imjacobestep/smart-study-lamp/tesseract example.jpg

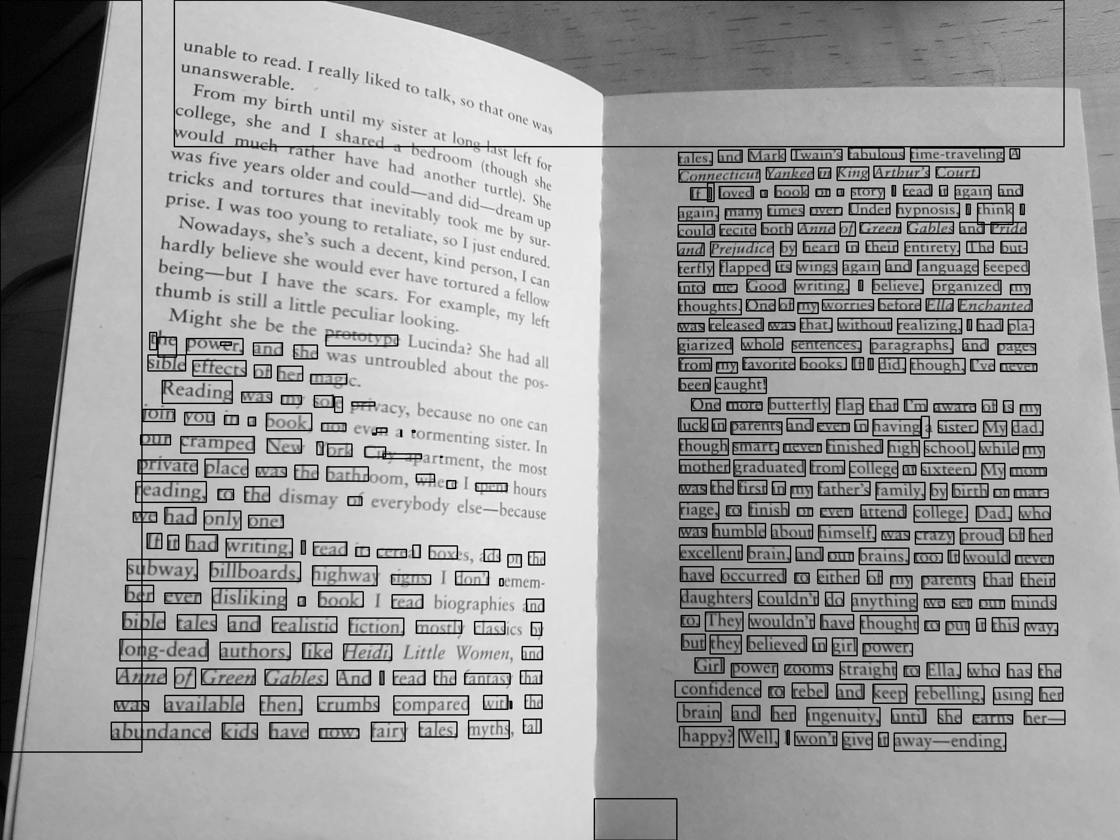
tesseract example.jpg
