imjacobestep/smart-study-lamp/test_code/past_camera_test/photos/images_crop/1.jpg

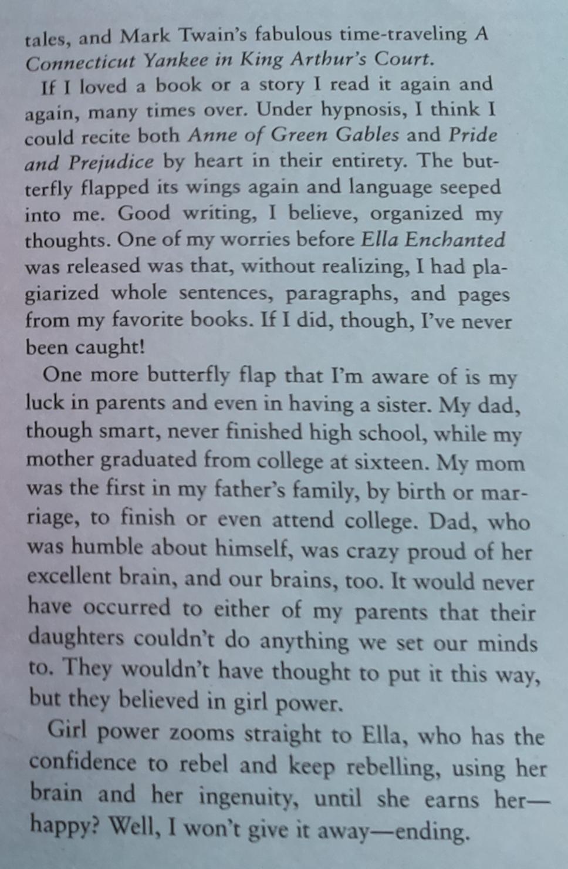
test_code/past_camera_test/photos/images_crop/1.jpg
