imjacobestep/smart-study-lamp/test_code/past_camera_test/photos/photos with lens 1/test5.jpg

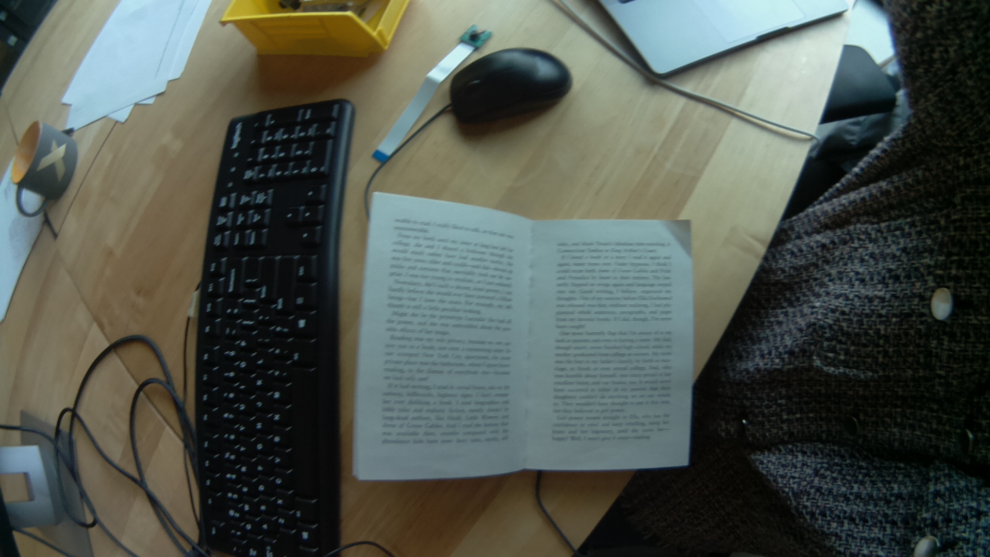
test_code/past_camera_test/photos/photos with lens 1/test5.jpg
