imjacobestep/smart-study-lamp/test_code/past_camera_test/photos/photos with lens 2/img0_stand.jpg

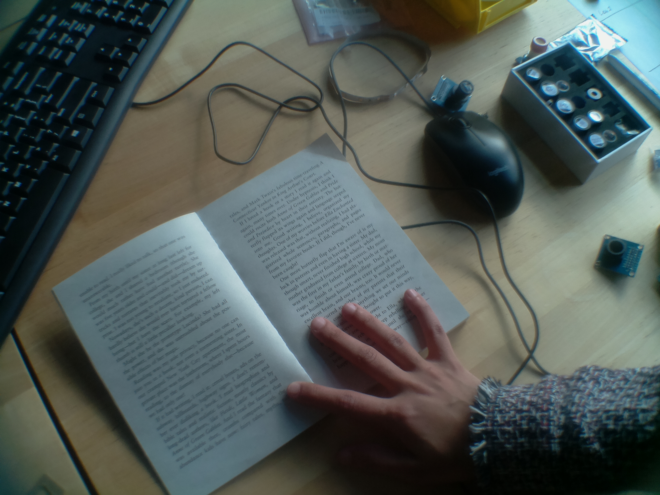
test_code/past_camera_test/photos/photos with lens 2/img0_stand.jpg
