imjacobestep/smart-study-lamp/test_code/past_camera_test/photos/photos with raspberry pi cam/img3_stand.jpg

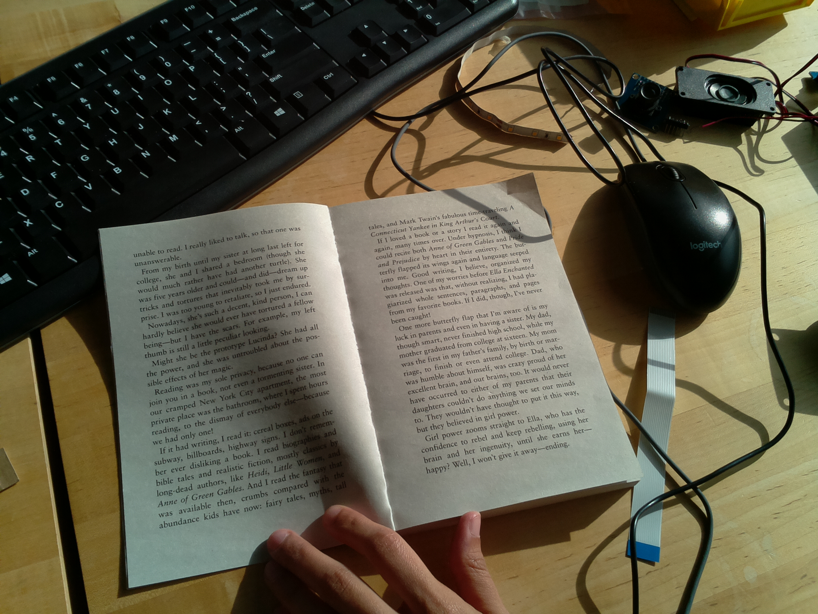
test_code/past_camera_test/photos/photos with raspberry pi cam/img3_stand.jpg
