imjacobestep/smart-study-lamp/test_code/past_camera_test/photos/photos with raspberry pi cam/test1.jpg

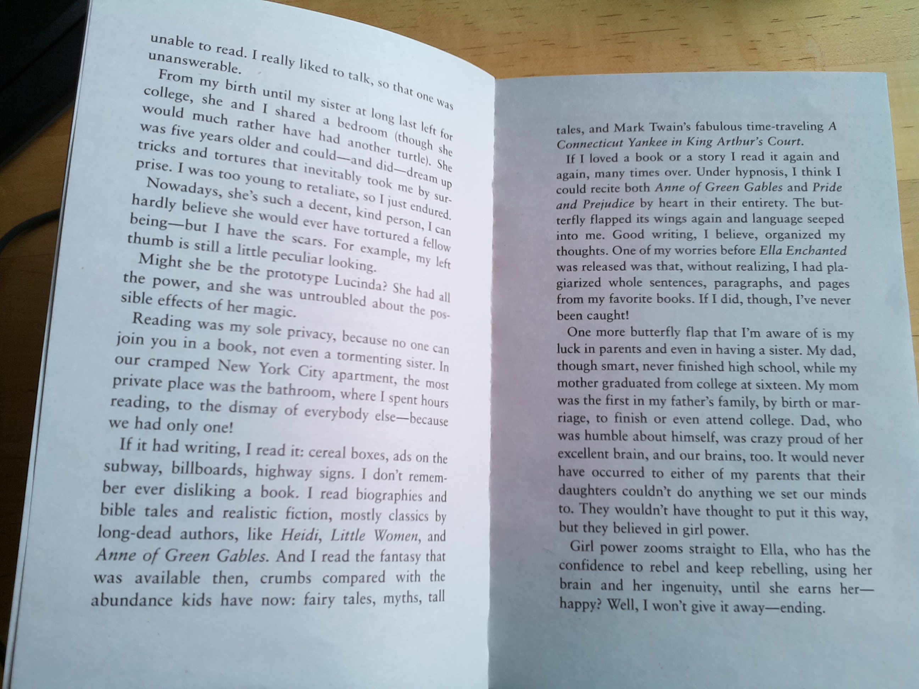
test_code/past_camera_test/photos/photos with raspberry pi cam/test1.jpg
