imjacobestep/smart-study-lamp/test_code/past_camera_test/photos/skew_test_images/p3.jpg

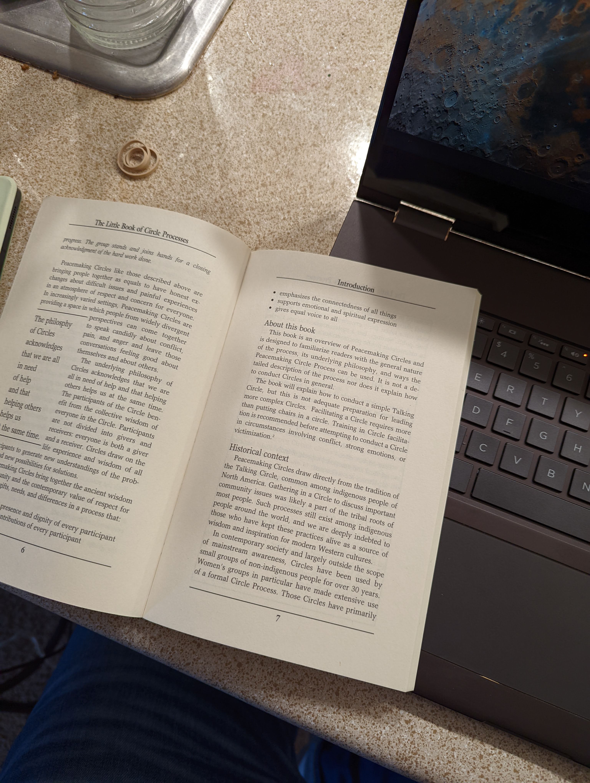
test_code/past_camera_test/photos/skew_test_images/p3.jpg
