imjacobestep/smart-study-lamp/test_code/definition_test.py

# DEFINITION TEST
from PyDictionary import PyDictionary
dictionary = PyDictionary

def define(word):
  return dictionary.meaning(word)

userIn = input("type word to define: ")
print(define(userIn)["Noun"][0])
